vaishnavi-p/Health-Performance-Monitoring-Fitness-Vest/Documentation/Miscellaneous/Accelorometer LIS3DH Current Consumption Table.png

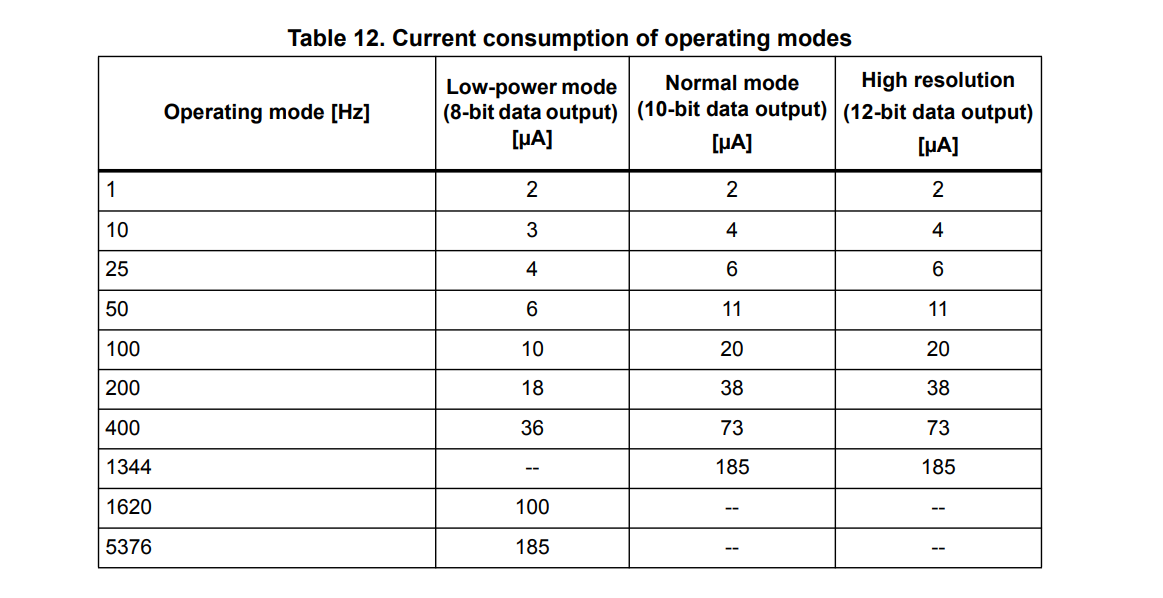
Documentation/Miscellaneous/Accelorometer LIS3DH Current Consumption Table.png
